sabrinabaungartner/Bebedero-vacas/Arduino/proyecto_final_bebederos/master_esp32/bt_handler.cpp

#include "bt_handler.h"
#include <Arduino.h>
#include "BluetoothSerial.h"
#include "package.h"

uint8_t rx_tx_buf[SIZE_ARRAY];
struct packet pac_to_send, my_received_packet_struct;
uint8_t received_array[SIZE_ARRAY]; 

#define USE_NAME // Comment this to use MAC address instead of a slave_name
#define LED_BT_BLUE 2 // LED onboard

// Check if Bluetooth is available
#if !defined(CONFIG_BT_ENABLED) || !defined(CONFIG_BLUEDROID_ENABLED)
  #error Bluetooth is not enabled! Please run `make menuconfig` to and enable it
#endif

// Check Serial Port Profile
#if !defined(CONFIG_BT_SPP_ENABLED)
  #error Serial Port Profile for Bluetooth is not available or not enabled. It is only available for the ESP32 chip.
#endif

BluetoothSerial SerialBT;

#ifdef USE_NAME
  String slave_name = "ESP32-BT-Slave"; // Name of slave BT device
#else
  uint8_t address[6]  = {0x26, 0x6F, 0x28, 0x17, 0x9F, 0x80}; // Slave MAC address 24:6F:28:17:9F:80
#endif

String master_name = "ESP32-BT-Master";
bool slave_is_connected = false;

// Callback function for Bluetooth
void callback(esp_spp_cb_event_t event, esp_spp_cb_param_t *param){
  if (event == ESP_SPP_OPEN_EVT) { // SPP Client connection open
    Serial.println("A SPP client opens a connectionT");
    digitalWrite(LED_BT_BLUE, HIGH);
    slave_is_connected = true;
  }

  if (event == ESP_SPP_CLOSE_EVT) { // SPP connection closed
    Serial.println("A SPP connection is closed");
    digitalWrite(LED_BT_BLUE, LOW);
    slave_is_connected = false;
  }
}

void setup_bluetooth_configuration() {
  pinMode(LED_BT_BLUE, OUTPUT);

  SerialBT.register_callback(callback);

  SerialBT.begin(master_name, true);
  Serial.printf("The device \"%s\" started in master mode, make sure slave BT device is on!\n", master_name.c_str());

  #ifndef USE_NAME
    SerialBT.setPin(pin);
  #endif

  if (!connect_to_slave()) {
    Serial.println("Failed to connect. Make sure remote device is available and in range, then restart app.");
  }
}

bool connect_to_slave() {
  #ifdef USE_NAME
    slave_is_connected = SerialBT.connect(slave_name);
  #else
    slave_is_connected = SerialBT.connect(address);
  #endif
  return slave_is_connected;
}

void send_via_bt(uint8_t array[], uint8_t size_array) {
  SerialBT.write(array, size_array);
}

void send_package() {
  packet_to_send(&pac_to_send, rx_tx_buf);
  send_via_bt(rx_tx_buf, sizeof(rx_tx_buf));
}

void create_package_to_send(uint8_t size, uint8_t message, uint8_t value) {
  pac_to_send.length = size;
  pac_to_send.type_of_message = message;
  pac_to_send.payload[0] = value;
  pac_to_send.payload[1] = value;
  pac_to_send.payload[2] = value;
  pac_to_send.payload[3] = value;
  pac_to_send.payload[4] = value;
  pac_to_send.payload[5] = value;
  pac_to_send.payload[6] = value;
}

bool check_slave_is_connected() {
  return slave_is_connected;
}

void request_to_slave(uint8_t request) {
  if (!slave_is_connected) {
    connect_to_slave();
  }
  else {
    switch(request) {
      case GET_WATER_LEVEL_AND_TEMPERATURE:
      Serial.println("requiero water level and temperature");
        create_package_to_send(SIZE_ARRAY, GET_WATER_LEVEL_AND_TEMPERATURE, NULO);
        send_package();
        break;
      case GET_WATER_LEVEL:
        create_package_to_send(SIZE_ARRAY, GET_WATER_LEVEL, NULO);
        send_package();
        break;
      case TURN_ON_PUMP:
        create_package_to_send(SIZE_ARRAY, TURN_ON_PUMP, NULO);
        send_package();
        break;
      case TURN_OFF_PUMP:
        create_package_to_send(SIZE_ARRAY, TURN_OFF_PUMP, NULO);
        send_package();
        break;
    }
  }
}

int receive_requested_water_level() {
  int reconstructed_value = 0;
  for (size_t i = 0; i < sizeof(int); i++) { // i goes from 0 to 4
    reconstructed_value |= (my_received_packet_struct.payload[i] << (i * 8));
  }

  return reconstructed_value;
}

float receive_requested_water_temperature() {
  uint8_t entera_uint8 = my_received_packet_struct.payload[4];
  uint8_t decimal_uint8 = my_received_packet_struct.payload[5];

  float entera_uint8_float = static_cast<float>(entera_uint8);
  float decimal_uint8_float = static_cast<float>(decimal_uint8) / 100;

  float float_number = entera_uint8_float + decimal_uint8_float;
  return float_number;
}

void receive_from_slave() {
  uint8_t index = 0;
  while (SerialBT.available() && (index < SIZE_ARRAY)) {
    received_array[index++] = SerialBT.read();
  }

  received_packet(&my_received_packet_struct, received_array);
}

uint8_t get_message_received() {
  return my_received_packet_struct.type_of_message;
}
