sabrinabaungartner/Bebedero-vacas/Arduino/proyecto_final_bebederos/master_esp32/package.cpp

#include <stdint.h>
#include "package.h"

void packet_to_send(struct packet * pac, uint8_t array[SIZE_ARRAY]) {
  array[0] = START_PACKET;
  array[1] = pac->length;
  array[2] = pac->type_of_message;
  array[3] = pac->payload[0];
  array[4] = pac->payload[1];
  array[5] = pac->payload[2];
  array[6] = pac->payload[3];
  array[7] = pac->payload[4];
  array[8] = pac->payload[5];
  array[9] = pac->payload[6];
  array[10] = END_PACKET;
}

void received_packet(struct packet * pac, uint8_t array[SIZE_ARRAY]) {
  if ((array[0] == START_PACKET) && (array[10] == END_PACKET) && (array[1] == SIZE_ARRAY)) {
    pac->length = array[1];
    pac->type_of_message = array[2];
    pac->payload[0] = array[3];
    pac->payload[1] = array[4];
    pac->payload[2] = array[5];
    pac->payload[3] = array[6];
    pac->payload[4] = array[7];
    pac->payload[5] = array[8];
    pac->payload[6] = array[9];
  }
}
